Juliexiaoni/Projet-S6/Core/Inc/LED.h

/*
 * LED.h
 *
 *  Created on: Mar 13, 2025
 *      Author: juliexiaoni
 */

#ifndef INC_LED_H_
#define INC_LED_H_

#include "stm32g4xx_hal.h"

void LED_ON_minute(void);
void LED_ON_hour();
void LED_OFF();

#endif /* INC_LED_H_ */
