Juliexiaoni/Projet-S6/Core/Inc/utils.h

/*
 * utils.h
 *
 *  Created on: Mar 17, 2025
 *      Author: juliexiaoni
 */

#ifndef SRC_UTILS_H_
#define SRC_UTILS_H_

void loop();
void setup();
void calculate_angle(float *current_angle, int *start_angle);

#endif /* SRC_UTILS_H_ */
